LeoKnopGIT/DualSlopeADC/dual_slope_adc_pos.asc

C1: cap; 1n; V=50 Irms=0 Rser=0 Lser=0 mfg="Murata" pn="GCM1555C1H131JA16" type="C0G"
MC1: voltage; PULSE(0 3.3 0 10n 10n 160u 400u 100)
R1: res; 100k
R2: res; 5Meg
R3: res; 10k
U1: LTC6752
U3: ADG419
U5: AD8605
V1: voltage; 3.3
V2: voltage; 5
Vin: voltage; 2
Named nets: 0, GPIO1, Vin, Vdd, Vref, out
.tran 0 10m 0
