LeoKnopGIT/DualSlopeADC/dual_slope_adc.asc

C1: cap; 30n
D1: diode; 1N914
M1: nmos
M2: nmos4
M3: pmos4
M4: pmos
MC1: voltage; PULSE(3.3 0 0 1n 1n 1m 10m 100)
MC2: voltage; PULSE(3.3 0 1m 1n 1n 9m 10m 100)
MC3: voltage; PULSE(0 3.3 6m 1n 1n 1m 7m 1)
Q1: pnp
Q2: npn
R1: res; 100k
R2: res; 1k
R3: res; 10k
R4: res; 10k
R5: res; 100
R6: res; 10k
R7: res; 0
R8: res; 0
R9: res; 1000k
R10: res; 1k
U1: LTC6244
U3: LTC6244
U4: LTC6752
U5: LTC6244
V2: voltage; 3.3
V3: voltage; 3.3
V4: voltage; PULSE(3.3 -3.3 0 1n 1n 25u 50u 100)
V5: voltage; PULSE(-3.3 3.3 0 1n 1n 25u 50u 100)
Vin: voltage; 1
Named nets: 0, GPIO1, Vin, Vref, Vref_neg, GPIO2, out, GPIO3
.tran 0 100m 0 0.1m
Komperator
Eingangsstufe
