LeoKnopGIT/DualSlopeADC/Software/CH32V003F4P6/User/init.h

#ifndef INIT_H
#define INIT_H

#include "debug.h"
void init_USARTx_CFG(void);
void init_GPIO_display(void);
void init_GPIO_INT(void);
void init_Timer1(uint16_t prsc, uint16_t arr);
void init_Timer2(uint16_t prsc, uint16_t arr);
void initADC(void);
#endif 
